eldstal/touchless-xm/firmware/tobo/include/gestures.hpp

#pragma once

#include <stdint.h>


/* These are tweaks to the gesture timing
 * If the swipes don't work on your headset,
 * try tweaking these. The values are all milliseconds.
 */

#define MS_HOLD_CHECK 10

#define MS_TAP_DOWN 100
#define MS_TAP_UP 100
#define MS_TAP_LONG 2500

#define MS_SWIPE_OVERLAP 10
#define MS_SWIPE_PASS 60
#define MS_SWIPE_REPEAT 200




struct gesture;
typedef struct gesture gesture_t;

// A state machine implementing a gesture
// Returns -1 when the gesture is completed
typedef int16_t (*gesture_func_t)(const gesture_t* gesture, bool trigger, int16_t state);

struct gesture {
    gesture_func_t func;
    uint8_t n_pins;
    uint8_t pin[4];
};



/*
 * Perform a gesture
 */
extern void gesture_perform(const gesture_t* gesture, uint8_t trigger_pin);

/*
 * Predefined gestures which we can trigger
 */ 

// Do nothing
extern const gesture_t GESTURE_NOP;

// Nothing, probably
extern const gesture_t GESTURE_TAP;

// Play/pause
extern const gesture_t GESTURE_DOUBLE_TAP;

// Voice assistant
extern const gesture_t GESTURE_TAP_AND_HOLD;

// Listen to surroundings
extern const gesture_t GESTURE_PALM;

// Toggle speak-to-chat
extern const gesture_t GESTURE_TWO_FINGER_LONG;

// FFWD
extern const gesture_t GESTURE_SWIPE_FWD;

// REV
extern const gesture_t GESTURE_SWIPE_BWD;

// Volume up
extern const gesture_t GESTURE_SWIPE_UP;

// Volume down
extern const gesture_t GESTURE_SWIPE_DOWN;
